ranieriv/HIVIS2/server/website/images/Caricatura.jpg

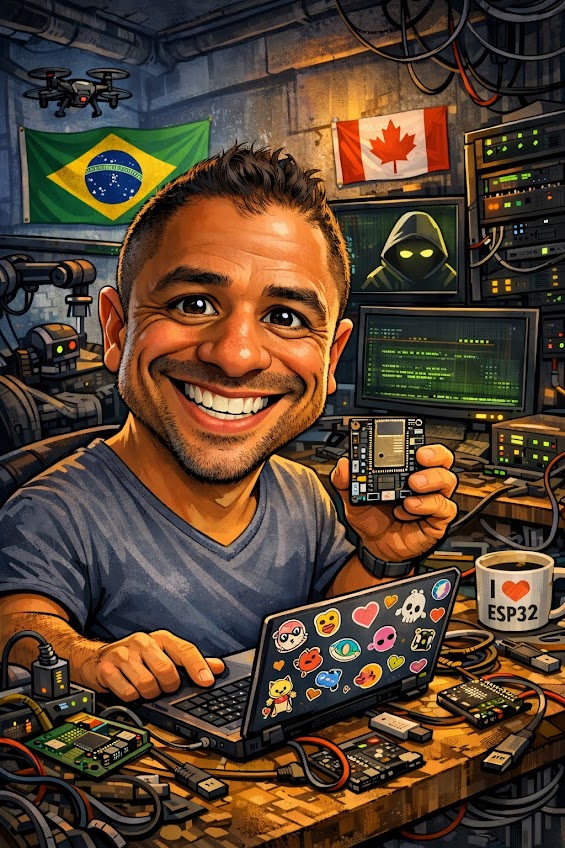
server/website/images/Caricatura.jpg
