ranieriv/HIVIS2/server/website/images/HIVIS2Final.png

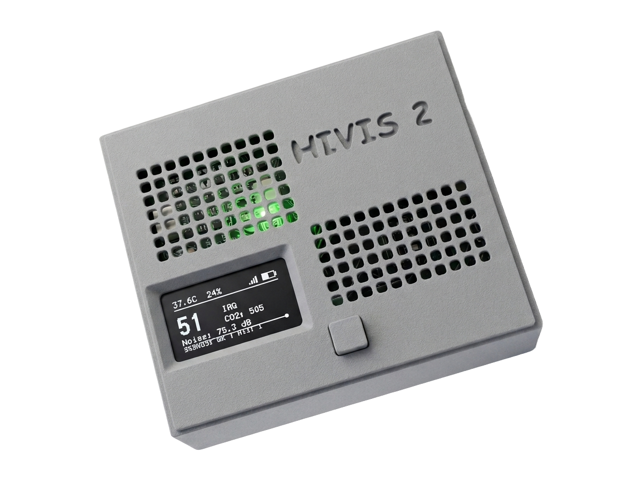
server/website/images/HIVIS2Final.png
