ranieriv/HIVIS2/server/website/images/HIVIS_Worker_2.png

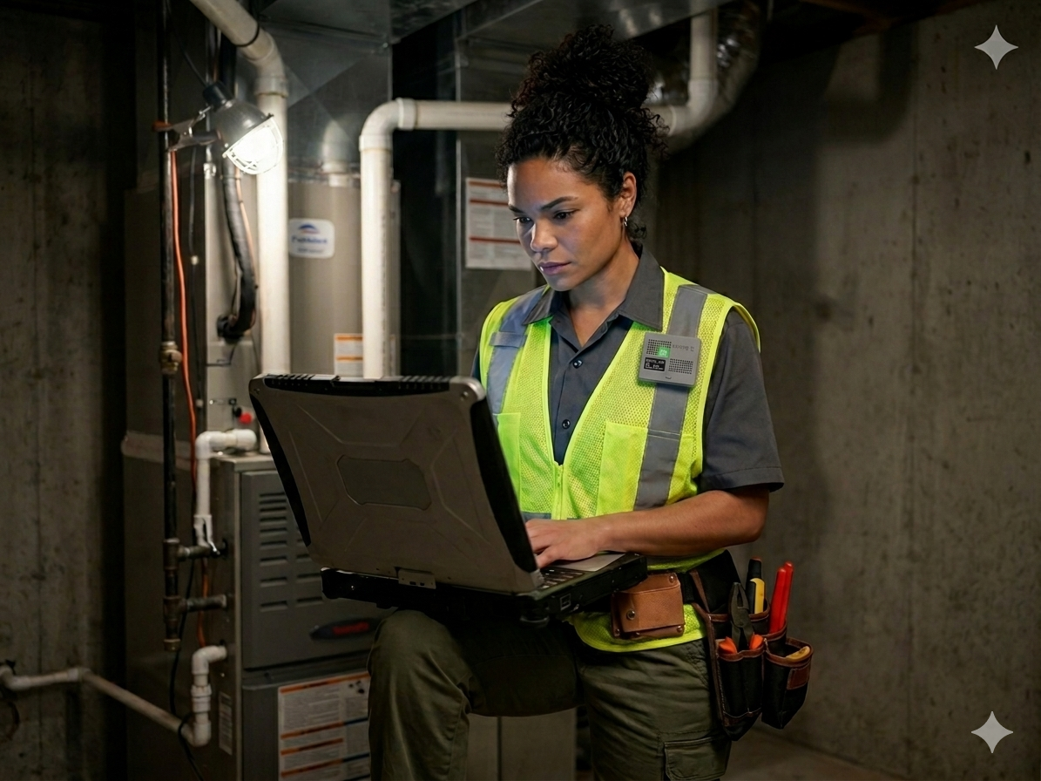
server/website/images/HIVIS_Worker_2.png
