ranieriv/HIVIS2/server/website/images/IMG_5893.jpg

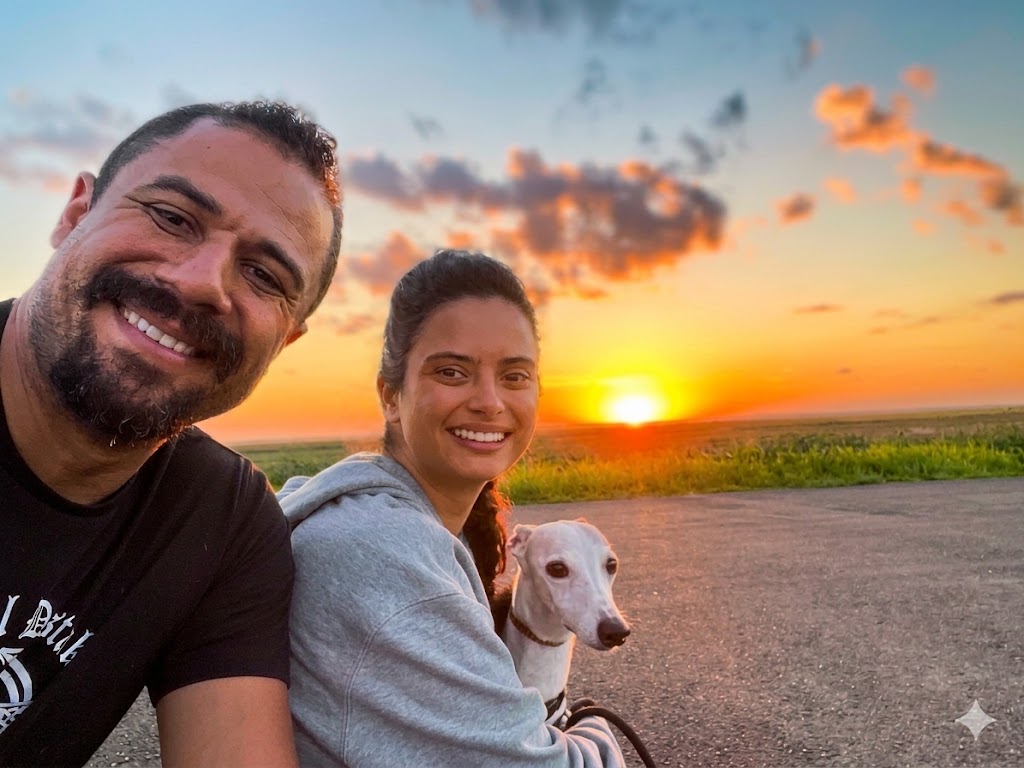
server/website/images/IMG_5893.jpg
