ranieriv/HIVIS2/server/website/images/ShieldHIVIS.png

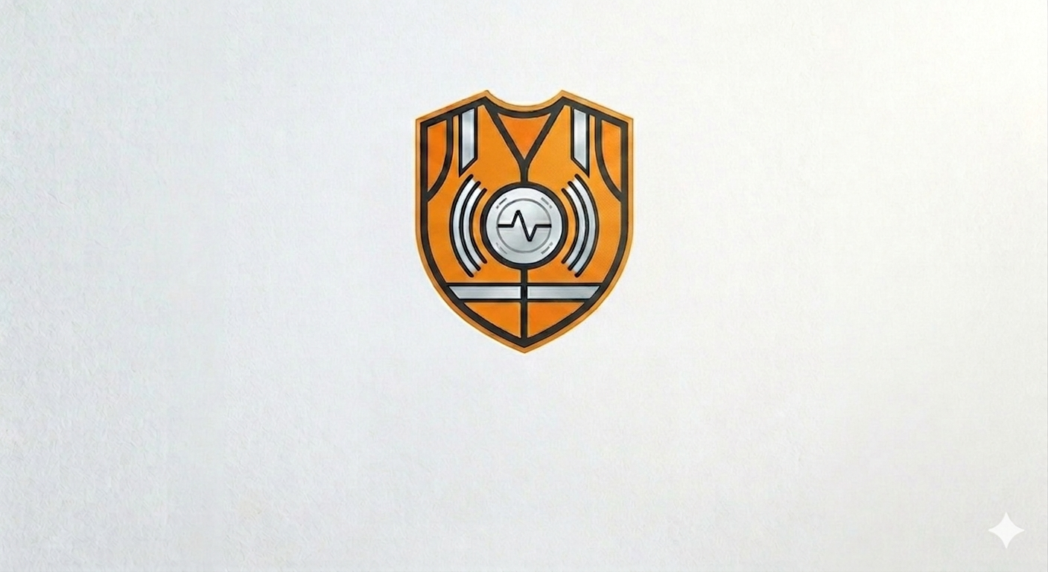
server/website/images/ShieldHIVIS.png
